Circuit-Digest/Digital-Ludo-board/Images/IMG_0026.jpg

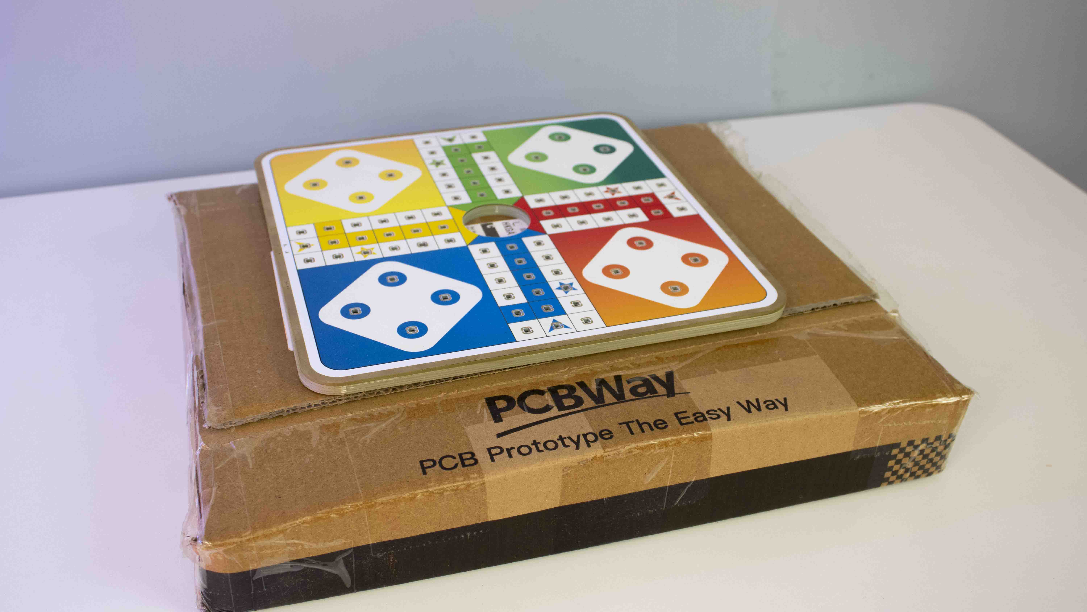
Images/IMG_0026.jpg
