Circuit-Digest/Digital-Ludo-board/Images/IMG_0028.jpg

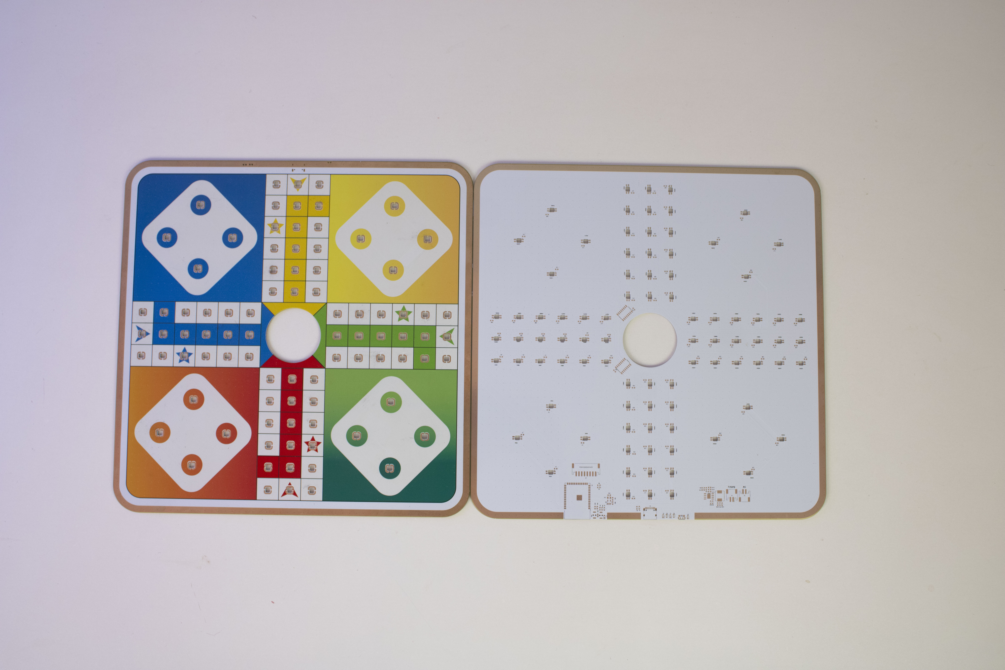
Images/IMG_0028.jpg
