Circuit-Digest/Digital-Ludo-board/Images/IMG_0029.jpg

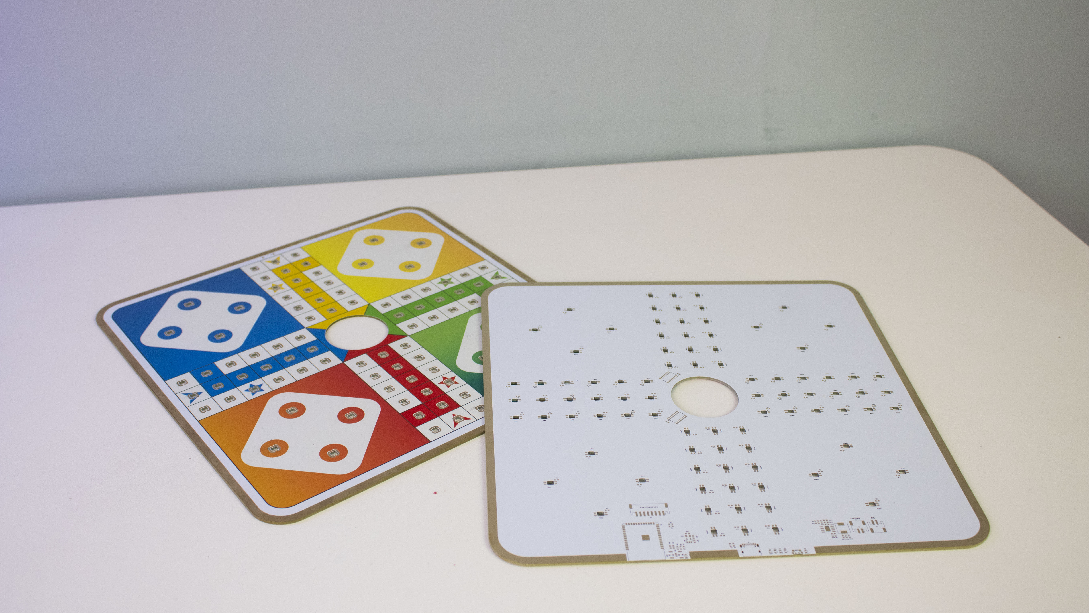
Images/IMG_0029.jpg
