Circuit-Digest/Digital-Ludo-board/Images/IMG_0030.jpg

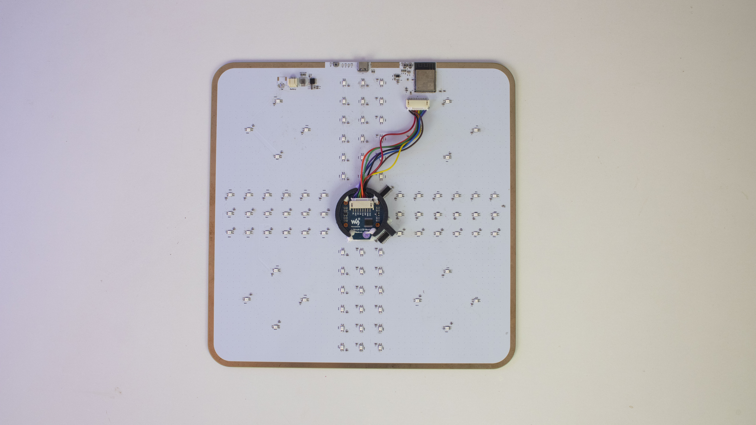
Images/IMG_0030.jpg
