Circuit-Digest/Digital-Ludo-board/Images/IMG_0031.jpg

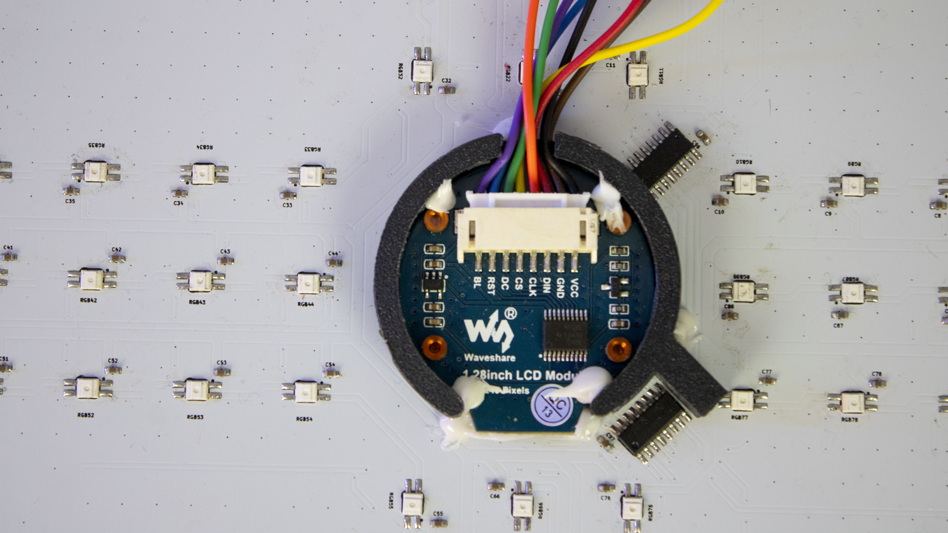
Images/IMG_0031.jpg
