Circuit-Digest/Digital-Ludo-board/Images/IMG_0034.jpg

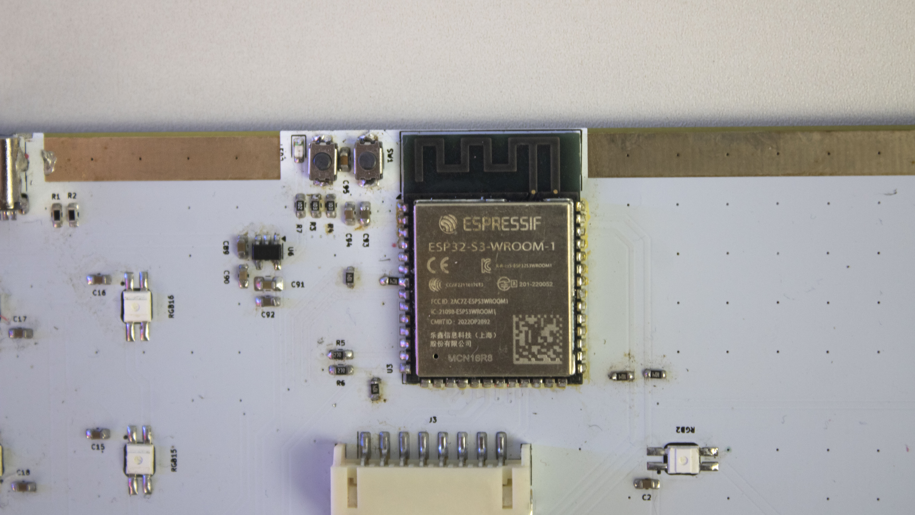
Images/IMG_0034.jpg
