Circuit-Digest/Digital-Ludo-board/Images/LUDO Enclousure 3D.png

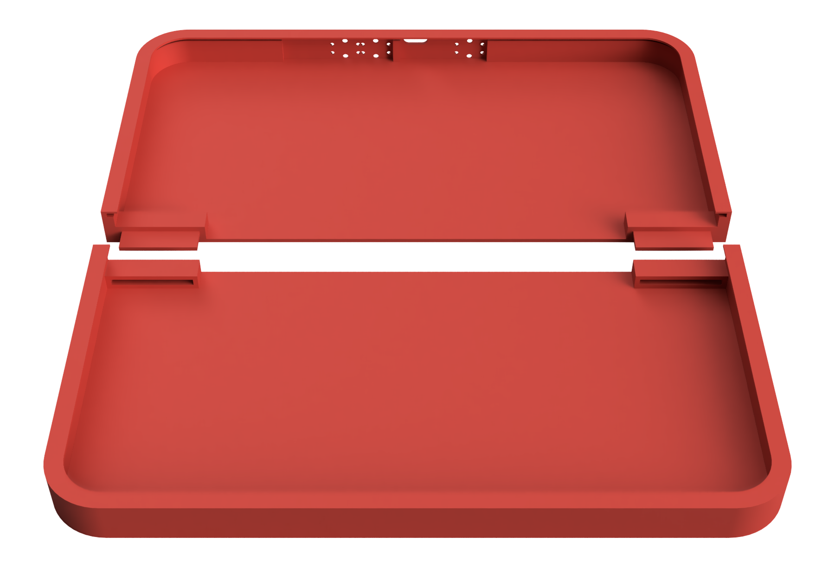
Images/LUDO Enclousure 3D.png
