Circuit-Digest/Digital-Ludo-board/Images/LUDO PCB 3D top and bottom.PNG

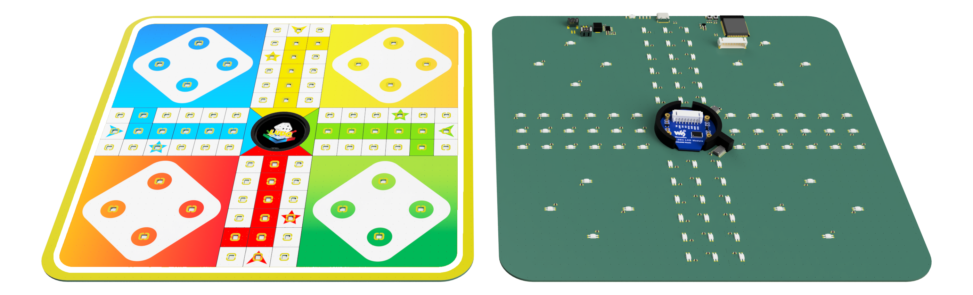
Images/LUDO PCB 3D top and bottom.PNG
