Circuit-Digest/Digital-Ludo-board/Images/LudoBoard PCB 3D View Top.png

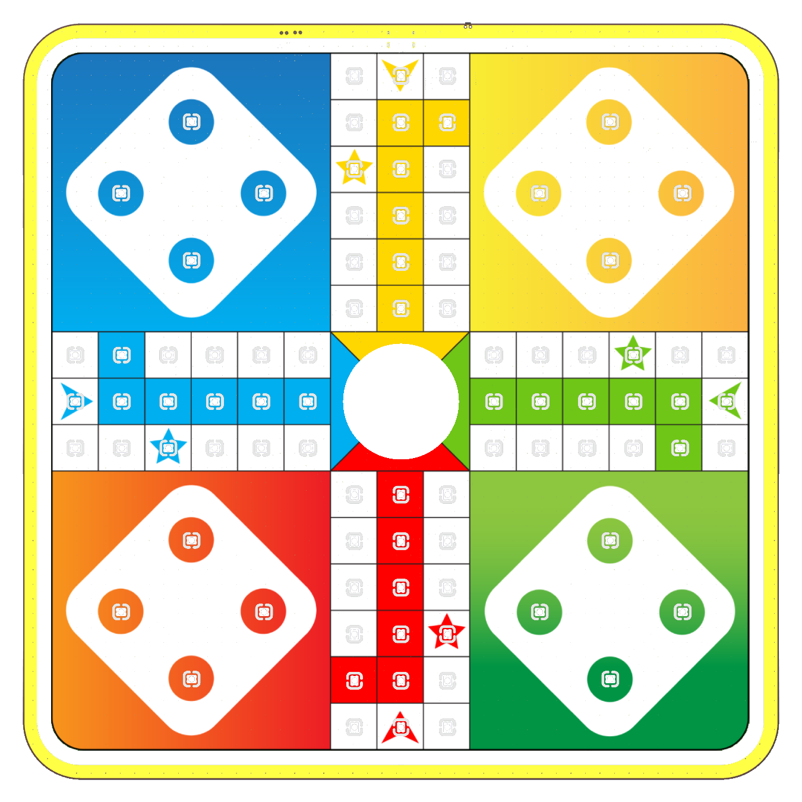
Images/LudoBoard PCB 3D View Top.png
