Circuit-Digest/Digital-Ludo-board/Images/LudoBoard PCB 3D View.png

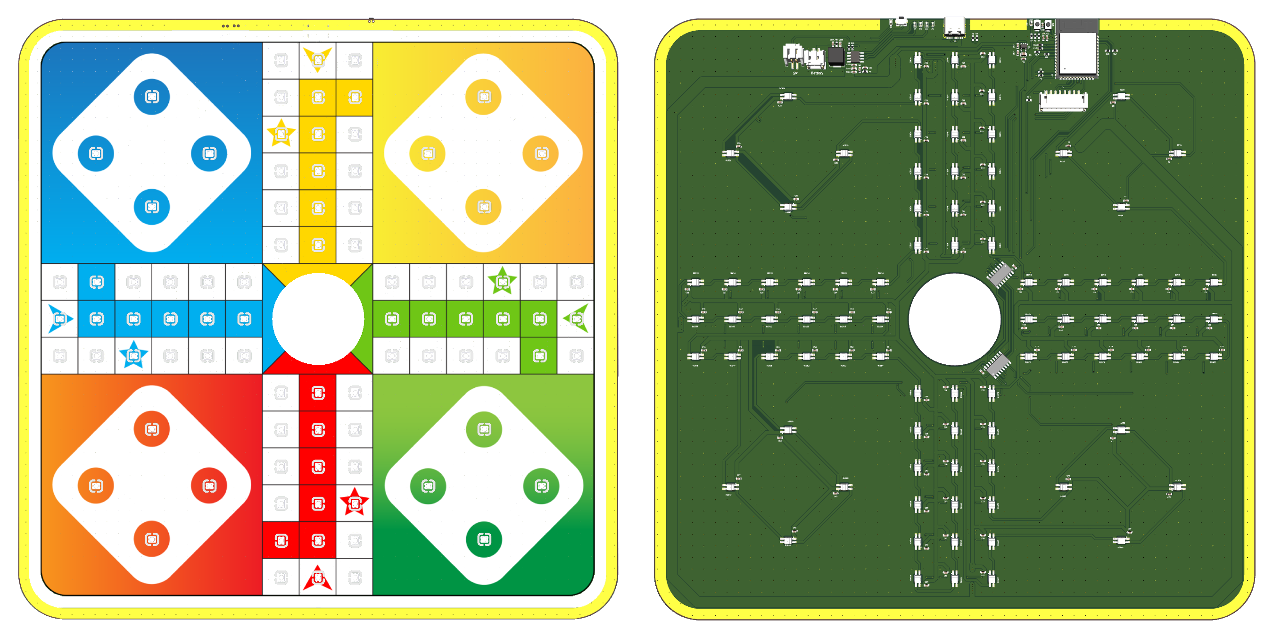
Images/LudoBoard PCB 3D View.png
