Circuit-Digest/Digital-Ludo-board/Images/LudoBoard PCB Bottom Layer.png

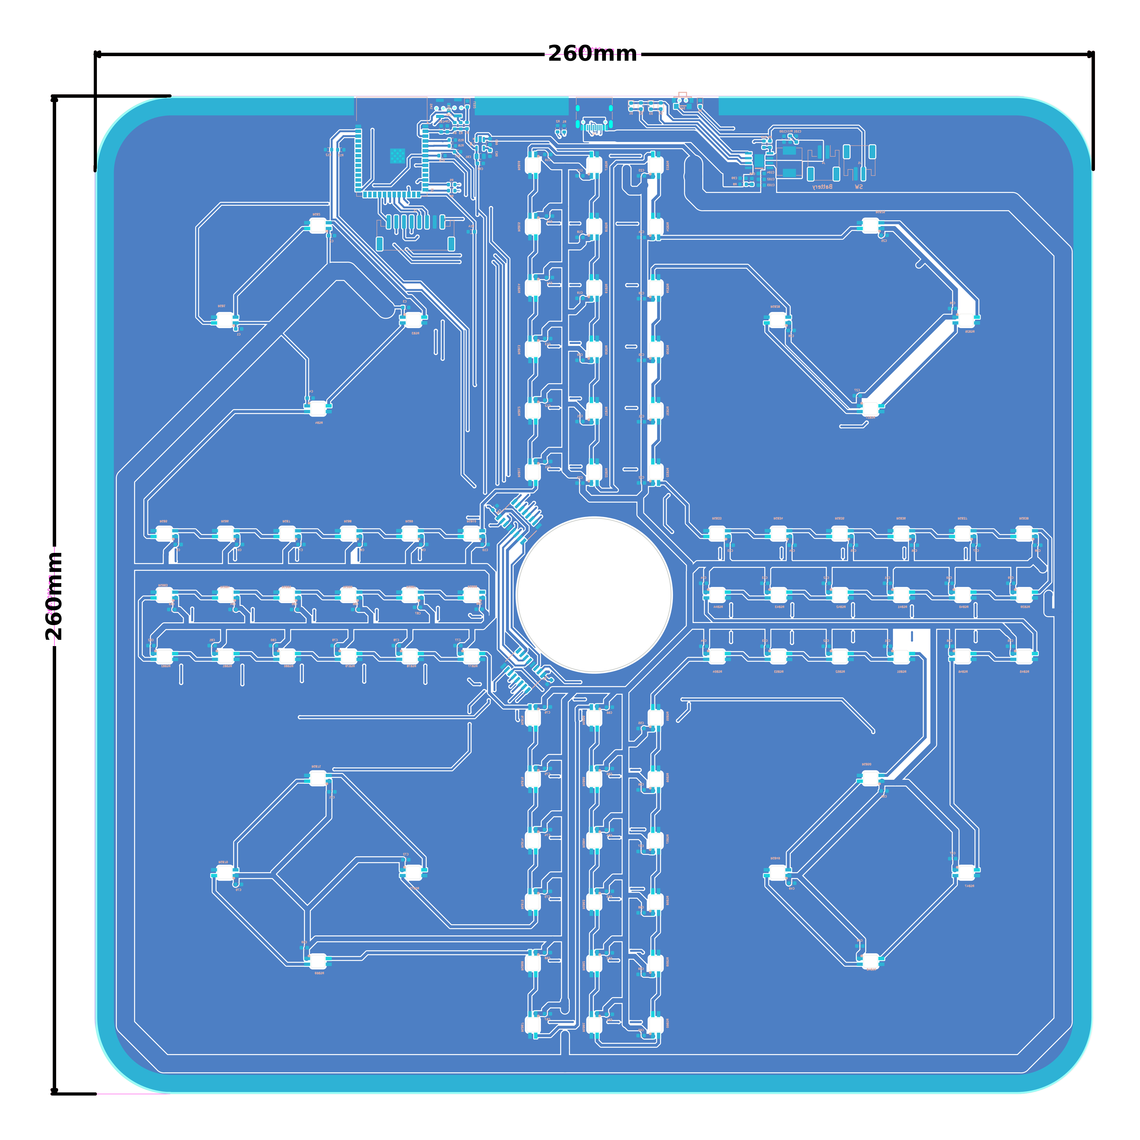
Images/LudoBoard PCB Bottom Layer.png
