Circuit-Digest/Digital-Ludo-board/Images/LudoBoard PCB Layer.png

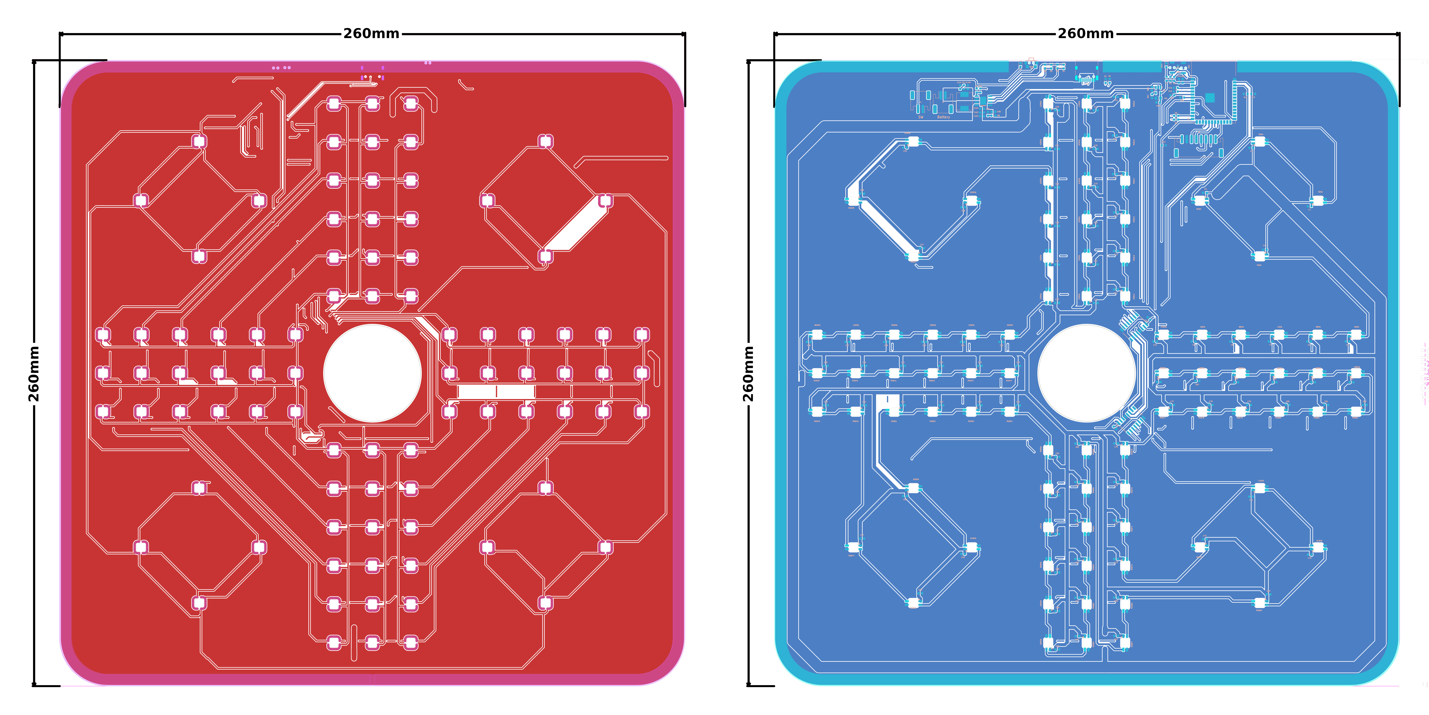
Images/LudoBoard PCB Layer.png
