Circuit-Digest/Digital-Ludo-board/Images/LudoBoard PCB Layer.png.png

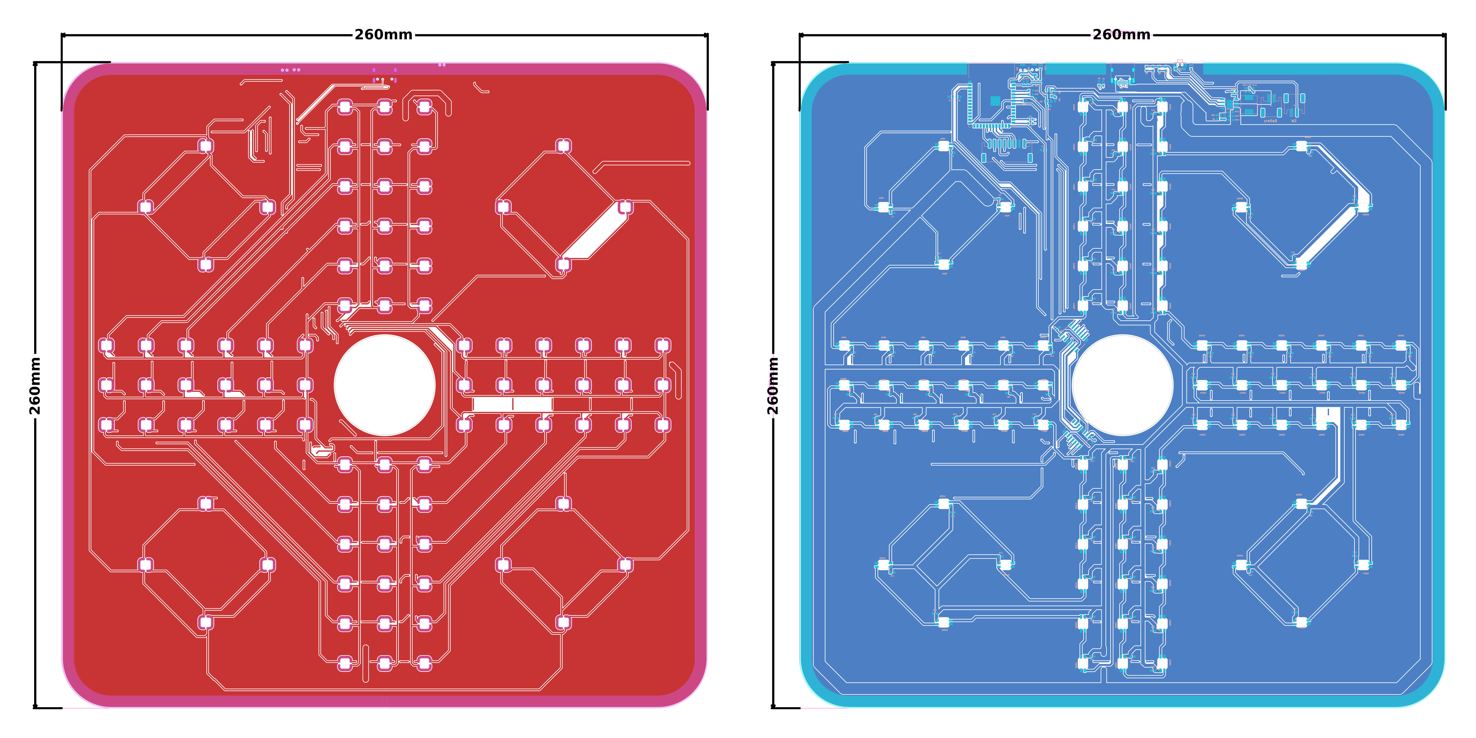
Images/LudoBoard PCB Layer.png.png
