Circuit-Digest/Digital-Ludo-board/Images/LudoBoard PCB Top Layer.png

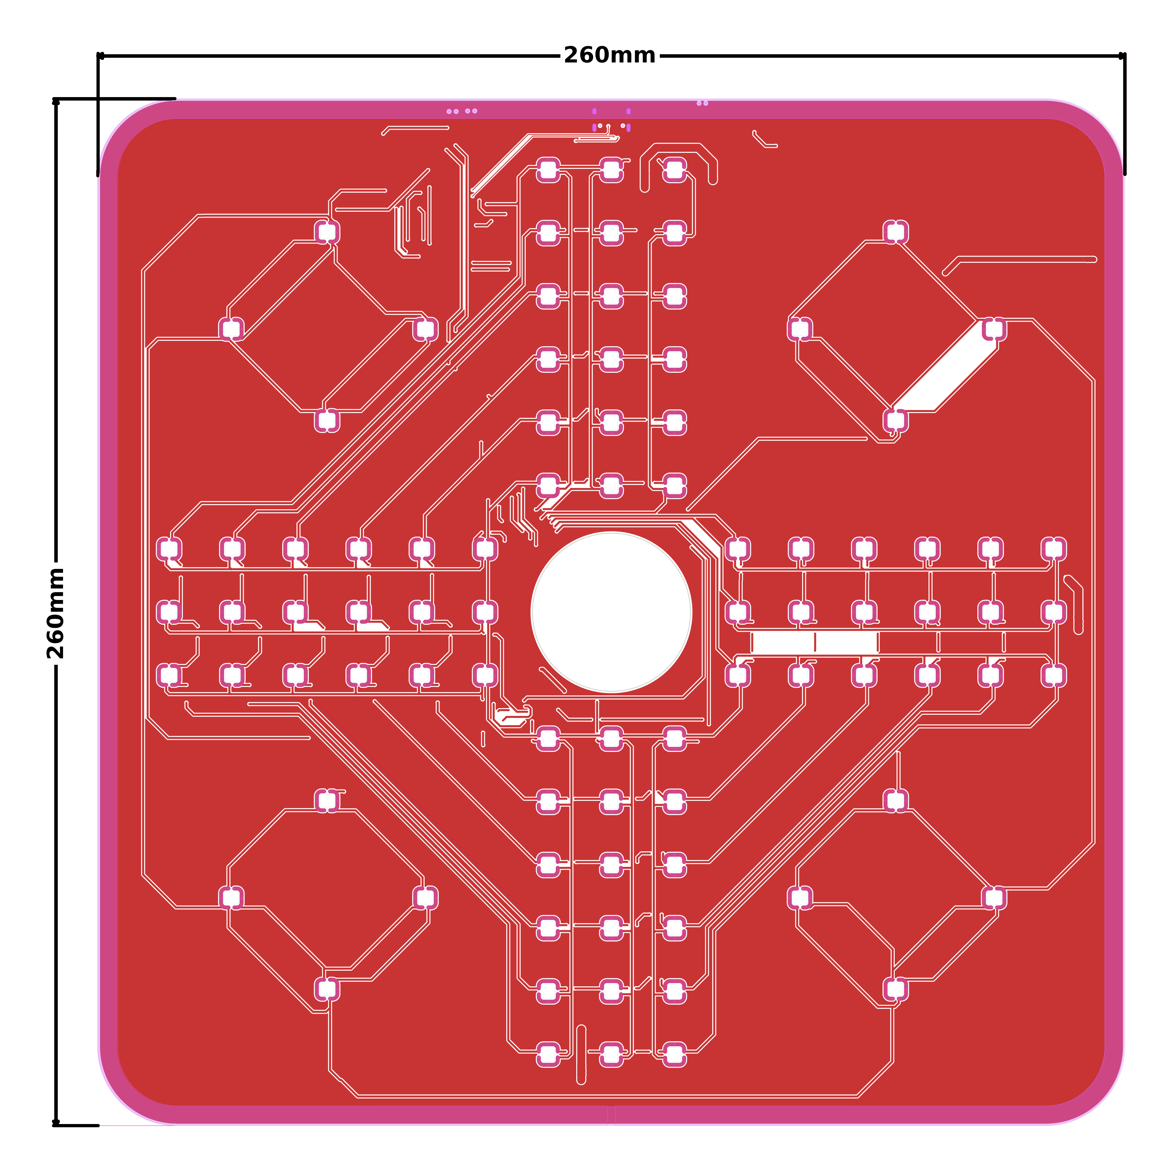
Images/LudoBoard PCB Top Layer.png
